akielaries/signalmesh/modules/apm/bsp/bsp.c

#include <stddef.h>

#include "hal.h"
#include "ch.h"

#include "bsp/bsp.h"

#include "bsp/utils/bsp_gpt.h"
#include "bsp/utils/bsp_io.h"

#include "bsp/configs/bsp_uart_config.h"
#include "bsp/configs/bsp_i2c_config.h"
#include "bsp/configs/bsp_spi_config.h"

#include "drivers/driver_registry.h"
#include "drivers/driver_api.h"

#include "drivers/ina219.h"
#include "drivers/ina3221.h"
#include "drivers/bme280.h"
#include "drivers/bh1750.h"
#include "drivers/aht2x.h"
#include "drivers/24lc256.h"
#include "drivers/w25qxx.h"
#include "drivers/servo.h"
#include "drivers/gm009605.h"
#include "drivers/lcd2004.h"

#include "version_gen.h" // generated: FW_VERSION_STRING etc.



// private data for ina219
static ina219_t ina219_dev_data[2];
// private data for ina3221
static ina3221_t ina3221_dev_data;
// private data for bme280
// static bme280_t bme280_dev_data; // BME280 driver doesn't have a private data struct
// private data for bh1750
static bh1750_t bh1750_dev_data;
static aht2x_t aht2x_dev_data;
static eeprom_24lc256_t eeprom_24lc256_dev_data;
// private data for w25qxx
static w25qxx_t w25qxx_dev_data_1;
static w25qxx_t w25qxx_dev_data_2;
// private data for servo
// static servo_t servo_dev_data; // servo driver doesn't have a private data struct
// private data for gm009605
static gm009605_t gm009605_dev_data;
static lcd2004_t lcd2004_dev_data;


// array of devices present on APM
device_t board_devices[] = {
    {
        .name = "ina219_main",
        .driver = &ina219_driver,
        .bus = &I2CD1,
        .addr = 0x40,
        .priv = &ina219_dev_data[0],
        .is_active = true
    },
    {
        .name = "ina219_aux",
        .driver = &ina219_driver,
        .bus = &I2CD1,
        .addr = 0x45, // A0 and A1 pins grounded
        .priv = &ina219_dev_data[1],
        .is_active = true
    },
    {
        .name = "ina3221",
        .driver = &ina3221_driver,
        .bus = &I2CD1,
        .addr = 0x40, // Note: This may conflict with ina219_main
        .priv = &ina3221_dev_data,
        .is_active = false
    },
    {
        .name = "aht2x",
        .driver = &aht2x_driver,
        .bus = &I2CD1,
        .addr = 0x38,
        .priv = &aht2x_dev_data,
        .is_active = false
    },
    {
        .name = "bme280",
        .driver = &bme280_driver,
        .bus = &I2CD1,
        .addr = 0x76,
        .priv = NULL,
        .is_active = false
    },
    {
        .name = "bh1750",
        .driver = &bh1750_driver,
        .bus = &I2CD1,
        .addr = 0x23,
        .priv = &bh1750_dev_data,
        .is_active = false
    },
    {
        .name = "24lc256",
        .driver = &eeprom_24lc256_driver,
        .bus = &I2CD1,
        .addr = 0x50,
        .priv = &eeprom_24lc256_dev_data,
        .is_active = false
    },
    {
        .name = "w25qxx_1",
        .driver = &w25qxx_driver,
        .bus = &spi_bus_w25qxx_1,
        .addr = 0, // SPI uses CS pin, not address
        .priv = &w25qxx_dev_data_1,
        .is_active = false
    },
    {
        .name = "w25qxx_2",
        .driver = &w25qxx_driver,
        .bus = &spi_bus_w25qxx_2,
        .addr = 0, // SPI uses CS pin, not address
        .priv = &w25qxx_dev_data_2,
        .is_active = false
    },
    {
        .name = "gm009605",
        .driver = &gm009605_driver,
        .bus = &I2CD1,
        .addr = 0x3C,
        .priv = &gm009605_dev_data,
        .is_active = true
    },
    {
        .name = "lcd2004",
        .driver = &lcd2004_driver,
        .bus = &I2CD1,
        .addr = 0x26,          // PCF8574 backpack on this module lands at 0x26 (not the 0x27 default)
        .priv = &lcd2004_dev_data,
        .is_active = true
    },
    /*
    {
        .name = "servo",
        .driver = &servo_driver,
        .bus = NULL,
        .priv = NULL,
        .is_active = false
    },
    */
};


// number of devices on APM
const size_t num_board_devices = sizeof(board_devices) / sizeof(board_devices[0]);


// onboard-LED heartbeat: a low-priority "is it alive" sweep over the three
// nucleo user LEDs. started by bsp_init, not from app main
static const ioline_t heartbeat_leds[] = {
  LINE_LED_GREEN,
  LINE_LED_YELLOW,
  LINE_LED_RED,
};

static THD_WORKING_AREA(wa_heartbeat, 256);
static THD_FUNCTION(heartbeat_thread, arg) {
  (void)arg;
  chRegSetThreadName("heartbeat");

  const size_t n = sizeof(heartbeat_leds) / sizeof(heartbeat_leds[0]);
  for (size_t i = 0; i < n; i++) {
    palSetLineMode(heartbeat_leds[i], PAL_MODE_OUTPUT_PUSHPULL);
    palClearLine(heartbeat_leds[i]);
  }

  // sweep one LED at a time so the cycle shows the scheduler is alive
  size_t cur = 0;
  while (true) {
    palSetLine(heartbeat_leds[cur]);
    chThdSleepMilliseconds(500);
    palClearLine(heartbeat_leds[cur]);
    cur = (cur + 1U) % n;
  }
}

static void heartbeat_start(void) {
  chThdCreateStatic(wa_heartbeat, sizeof(wa_heartbeat),
                    LOWPRIO, heartbeat_thread, NULL);
}


void bsp_init(void) {
  halInit();
  chSysInit();

  // initialize debug UART
  bsp_io_init();

  bsp_printf("\n...Starting...\n\n");
  bsp_printf("%s\n", FW_VERSION_STRING); // e.g. APM v1.0.0-7e98556-dirty

  bsp_printf("booting...");
  for (uint8_t i = 0; i < 3; i++) {
    bsp_printf(".");
    chThdSleepMilliseconds(250);
  }
  bsp_printf("\n");

  // chip info
  bsp_printf("System tick freq: %u Hz\n", CH_CFG_ST_FREQUENCY);
  bsp_printf("DBGMCU->IDCODE: 0x%08lX\r\n", DBGMCU->IDCODE);
  bsp_printf("REV_ID: 0x%X\r\nDEV_ID: 0x%X\n", DBGMCU->IDCODE >> 16,
                                            DBGMCU->IDCODE & 0xFFF);

  // initialize drivers this board supports
  bsp_i2c_init();
  bsp_printf("I2C initialized\n");

  bsp_spi_init();
  bsp_printf("SPI initialized\n");

  init_devices();
  bsp_printf("initialized devices\n");

/*
  // these should be configured more elegantly like how the i2c stuff is configured
  // ADC inputs
  palSetPadMode(GPIOB, 1, PAL_MODE_INPUT_ANALOG); // PB1, ADC channel 5
  palSetPadMode(GPIOA, 3, PAL_MODE_INPUT_ANALOG); // PA3, ADC channel 15
  palSetPadMode(GPIOC, 0, PAL_MODE_INPUT_ANALOG); // PC0, ADC channel 10
  palSetPadMode(GPIOC, 3, PAL_MODE_INPUT_ANALOG); // PC3, ADC channel 13

  // PWM on PE11, timer 1 channel 2?
  palSetPadMode(GPIOE, 11, PAL_MODE_ALTERNATE(1));
*/

  heartbeat_start();
  bsp_printf("heartbeat thread started\n");

  bsp_printf("End of BSP init\n\r\n");
}
