akielaries/signalmesh/modules/afm/mcu/bsp/drivers/inc/GOWIN_M1_spi.h

/*
 ******************************************************************************************
 * @file      GOWIN_M1_spi.h
 * @author    GowinSemicoductor
 * @device    Gowin_EMPU_M1
 * @brief     This file contains all the functions prototypes for the SPI firmware library.
 ******************************************************************************************
 */

/* Define to prevent recursive inclusion -------------------------------------*/
#ifndef GOWIN_M1_SPI_H
#define GOWIN_M1_SPI_H

#ifdef __cplusplus
 extern "C" {
#endif

/* Includes ------------------------------------------------------------------*/
#include "GOWIN_M1.h"

/** @addtogroup GOWIN_M1_StdPeriph_Driver
  * @{
  */
/** @addtogroup SPI
  * @{
  */

/******************************************************************************/
/*                  Serial Peripheral Interface (SPI)                         */
/******************************************************************************/
/* bit definitions for CTRL register */
#define SPI_CR_DIRECTION           ((uint32_t) 0x00000001)    /* DIRECTION              */
#define SPI_CR_PHASE               ((uint32_t) 0x00000002)    /* PHASE                  */
#define SPI_CR_POLARITY            ((uint32_t) 0x00000004)    /* POLARITY               */
#define SPI_CR_CLKSEL              ((uint32_t) 0x00000018)    /* CLKSEL                 */

/* bit definitions for STATUS register */
#define SPI_STATUS_ROE             ((uint32_t) 0x00000004)    /* Receive Overrun Error  */
#define SPI_STATUS_TOE             ((uint32_t) 0x00000008)    /* Transmit Overrun Error */
#define SPI_STATUS_TMT             ((uint32_t) 0x00000010)    /* Transmitting           */
#define SPI_STATUS_TRDY            ((uint32_t) 0x00000020)    /* Transmit Ready         */
#define SPI_STATUS_RRDY            ((uint32_t) 0x00000040)    /* Receive Ready          */
#define SPI_STATUS_ERR             ((uint32_t) 0x00000080)    /* Error                  */

/**
  * @}
  */

/** @defgroup SPI_Exported_Types
  * @{
  */

/* SPI InitTypeDef */
typedef struct
{
  uint8_t  DIRECTION;  // 0: msb first; 1: lsb first
  uint8_t  PHASE;      // 0: sample at posedge edge; 1: sample at negedge.
  uint8_t  POLARITY;   // 0: idle sclk low; 1: idle sclk high
  uint8_t  CLKSEL;     // clk div = (clksel + 1) * 2
}SPI_InitTypeDef;

/**
  * @}
  */

/** @defgroup SPI_Exported_Macros
  * @{
  */

/* Clock Selection */
#define CLKSEL_CLK_DIV_2   ((uint32_t) 0x00000000)  //CLK/2
#define CLKSEL_CLK_DIV_4   ((uint32_t) 0x00000001)  //CLK/4
#define CLKSEL_CLK_DIV_6   ((uint32_t) 0x00000002)  //CLK/6
#define CLKSEL_CLK_DIV_8   ((uint32_t) 0x00000003)  //CLK/8

#define SHIFT_DIR_MSB_FIRST      (0)
#define SHIFT_DIR_LSB_FIRST      (1)

#define SPI_CPOL_LO              (0) 
#define SPI_CPOL_HI              (1)

#define SPI_CPHA_POSEDGE         (0)
#define SPI_CPHA_NEGEDGE         (1)

/* Register Bit Position */
#define SPI_CR_DIRECTION_Pos   0   /* CTRL register DIRECTION bit position */
#define SPI_CR_PHASE_Pos       1   /* CTRL register PHASE bit position     */
#define SPI_CR_POLARITY_Pos    2   /* CTRL register POLARITY bit position  */
#define SPI_STATUS_ROE_Pos     2   /* STATUS register ROE bit position     */
#define SPI_STATUS_TOE_Pos     3   /* STATUS register TOE bit position     */
#define SPI_STATUS_TMT_Pos     4   /* STATUS register TMT bit position     */
#define SPI_STATUS_TRDY_Pos    5   /* STATUS register TRDY bit position    */
#define SPI_STATUS_RRDY_Pos    6   /* STATUS register RRDY bit position    */
#define SPI_STATUS_ERR_Pos     7   /* STATUS register ERR bit position     */

#define SPI_CR_CLKSEL_Pos     ((uint32_t) 0x00000003)    /* CTRL register CLKSEL Position */
#define SPI_CR_CLKSEL_Mask    ((uint32_t) 0x00000003)    /* CTRL register CLKSEL mask     */

#define SELECT_SPI            {SPI->SSMASK = 1;}
#define DESELECT_SPI          {SPI->SSMASK = 0;}


/**
  * @}
  */

/** @defgroup SPI_Exported_Functions
  * @{
  */

/**
  * @brief Initializes SPI
  */
extern void SPI_Init(SPI_InitTypeDef* SPI_InitStruct);

/**
  * @brief Sets Direction
  */
extern void SPI_SetDirection(void);

/**
  * @brief Clears Direction
  */
extern void SPI_ClrDirection(void);

/**
  * @brief Returns Direction
  */
extern uint32_t SPI_GetDirection(void);

/**
  * @brief Sets Phase
  */
extern void SPI_SetPhase(void);

/**
  * @brief Clears Phase
  */
extern void SPI_ClrPhase(void);

/**
  * @brief Returns Phase
  */
extern uint32_t SPI_GetPhase(void);

/**
  * @brief Returns Polarity
  */
extern uint32_t SPI_GetPolarity(void);

/**
  * @brief Clears Polarity
  */
extern void SPI_ClrPolarity(void);

/**
  * @brief Sets Polarity
  */
extern void SPI_SetPolarity(void);

/**
  * @brief Sets ClkSel
  */
extern void SPI_SetClkSel(uint32_t clksel);

/**
  * @brief Returns ClkSel
  */
extern uint32_t SPI_GetClkSel(void);

/**
  * @brief Reads transmit overrun error status
  */
extern FlagStatus SPI_GetToeStatus(void);

/**
  * @brief Reads receive overrun error status
  */
extern FlagStatus SPI_GetRoeStatus(void);

/**
  * @brief Reads transmitting status
  */
extern FlagStatus SPI_GetTmtStatus(void);

/**
  * @brief Reads transmit ready status
  */
extern FlagStatus SPI_GetTrdyStatus(void);

/**
  * @brief Reads receive ready status
  */
extern FlagStatus SPI_GetRrdyStatus(void);

/**
  * @brief Reads error status
  */
extern FlagStatus SPI_GetErrStatus(void);

/**
  * @brief Clears transmit overrun error status
  */
extern void SPI_ClrToeStatus(void);

/**
  * @brief Clear receive overrun error status
  */
extern void SPI_ClrRoeStatus(void);

/**
  * @brief Clears error status
  */
extern void SPI_ClrErrStatus(void);

/**
  * @brief Reads and Writes Byte Data
  */
extern uint8_t SPI_ReadWriteByte(uint8_t cmd);

/**
  * @brief Writes Data
  */
extern void SPI_WriteData(uint8_t data);

/**
  * @brief Reads Data
  */
extern uint8_t SPI_ReadData(void);

/**
  * @brief SPI_Slave Select
  */
extern  void SPI_Select_Slave(uint32_t Slave_address);

#ifdef __cplusplus
}
#endif

#endif /* GOWIN_M1_SPI_H */

/**
  * @}
  */

/**
  * @}
  */
