akielaries/signalmesh/modules/afm/rtl/sine_wave_gen.v

/*
 * Sine Wave Generator Example for Gowin FPGAs
 *
 * This module demonstrates how to generate a sine wave using Pulse Width
 * Modulation (PWM). It produces a 30 kHz sine wave from a 27 MHz master clock.
 *
 * IMPORTANT: The output of this module is a PWM signal. To see an analog
 * sine wave, you MUST connect an external low-pass RC filter to the
 * output pin (bank2_3v3_waveform). A 1k Ohm resistor followed by a
 * 3.3nF capacitor to ground is a good starting point.
 */

module sine_wave_gen (
  // --- Inputs ---
  input bank1_3v3_xtal_in, // Input clock from the crystal oscillator (27 MHz)
  input bank3_1v8_sys_rst, // Active-low reset

  // --- Outputs ---
  output bank1_3v3_xtal_route,
  output bank2_3v3_waveform // The PWM signal output
);

  // --- Port Aliases (standard Verilog via wire/assign) ---
  wire clk;
  wire rst_n;

  assign clk = bank1_3v3_xtal_in;
  assign bank1_3v3_xtal_route = bank1_3v3_xtal_in;
  assign rst_n = bank3_1v8_sys_rst;
  // --------------------------------------------------------

  // --- Phase Accumulator for LUT Index ---
  // This steps through the sine lookup table at a rate that produces
  // the desired output frequency.
  // F_out = (F_clk * Step_inc) / (2^32)
  // Step_inc = (F_out * 2^32) / F_clk
  //          = (30,000 * 2^32) / 27,000,000 = 4772186
  localparam PHASE_INCREMENT = 32'd4772186;
  
  reg [31:0] phase_accumulator;
  always @(posedge clk or negedge rst_n) begin
    if (!rst_n) begin
      phase_accumulator <= 32'd0;
    end else begin
      phase_accumulator <= phase_accumulator + PHASE_INCREMENT;
    end
  end

  // Use the top 8 bits of the accumulator as the address for our 256-entry table.
  wire [7:0] lut_address = phase_accumulator[31:24];


  // --- Sine Wave Lookup Table (LUT) ---
  // This is a 256-entry, 8-bit Read-Only Memory (ROM) that stores one
  // cycle of a sine wave. The values range from 0 to 255.
  reg [7:0] lut_value;
  always @(*) begin
    case (lut_address)
      8'd0:   lut_value = 8'd128;
      8'd1:   lut_value = 8'd131;
      8'd2:   lut_value = 8'd134;
      8'd3:   lut_value = 8'd137;
      8'd4:   lut_value = 8'd140;
      8'd5:   lut_value = 8'd143;
      8'd6:   lut_value = 8'd146;
      8'd7:   lut_value = 8'd149;
      8'd8:   lut_value = 8'd152;
      8'd9:   lut_value = 8'd155;
      8'd10:  lut_value = 8'd158;
      8'd11:  lut_value = 8'd161;
      8'd12:  lut_value = 8'd164;
      8'd13:  lut_value = 8'd167;
      8'd14:  lut_value = 8'd170;
      8'd15:  lut_value = 8'd173;
      8'd16:  lut_value = 8'd176;
      8'd17:  lut_value = 8'd179;
      8'd18:  lut_value = 8'd182;
      8'd19:  lut_value = 8'd185;
      8'd20:  lut_value = 8'd188;
      8'd21:  lut_value = 8'd190;
      8'd22:  lut_value = 8'd193;
      8'd23:  lut_value = 8'd196;
      8'd24:  lut_value = 8'd198;
      8'd25:  lut_value = 8'd201;
      8'd26:  lut_value = 8'd203;
      8'd27:  lut_value = 8'd206;
      8'd28:  lut_value = 8'd208;
      8'd29:  lut_value = 8'd211;
      8'd30:  lut_value = 8'd213;
      8'd31:  lut_value = 8'd215;
      8'd32:  lut_value = 8'd217;
      8'd33:  lut_value = 8'd219;
      8'd34:  lut_value = 8'd221;
      8'd35:  lut_value = 8'd223;
      8'd36:  lut_value = 8'd225;
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
      8'd249: lut_value = 8'd107;
      8'd250: lut_value = 8'd110;
      8'd251: lut_value = 8'd113;
      8'd252: lut_value = 8'd116;
      8'd253: lut_value = 8'd119;
      8'd254: lut_value = 8'd122;
      8'd255: lut_value = 8'd125;
      default: lut_value = 8'd128;
    endcase
  end

  // --- PWM Generator ---
  // This creates a high-frequency square wave whose duty cycle is
  // controlled by the value from the sine LUT.
  reg [7:0] pwm_counter;
  always @(posedge clk or negedge rst_n) begin
    if (!rst_n) begin
      pwm_counter <= 8'd0;
    end else begin
      // The counter continuously cycles from 0-255
      pwm_counter <= pwm_counter + 1'b1;
    end
  end

  // The output is high when the counter is less than the sine value.
  // This creates the variable duty cycle.
  assign bank2_3v3_waveform = (pwm_counter < lut_value);

endmodule
