akielaries/signalmesh/modules/acm/acm_fpga/rtl/sine_lut.v

// generated: 256-entry, one-period, 12-bit unsigned sine ROM (centered 2048)
module sine_lut (input wire [7:0] addr, output reg [11:0] data);
  always @(*) begin
    case (addr)
      8'd0  : data = 12'd2048;
      8'd1  : data = 12'd2098;
      8'd2  : data = 12'd2148;
      8'd3  : data = 12'd2199;
      8'd4  : data = 12'd2249;
      8'd5  : data = 12'd2299;
      8'd6  : data = 12'd2348;
      8'd7  : data = 12'd2398;
      8'd8  : data = 12'd2447;
      8'd9  : data = 12'd2497;
      8'd10 : data = 12'd2545;
      8'd11 : data = 12'd2594;
      8'd12 : data = 12'd2642;
      8'd13 : data = 12'd2690;
      8'd14 : data = 12'd2738;
      8'd15 : data = 12'd2785;
      8'd16 : data = 12'd2831;
      8'd17 : data = 12'd2878;
      8'd18 : data = 12'd2923;
      8'd19 : data = 12'd2968;
      8'd20 : data = 12'd3013;
      8'd21 : data = 12'd3057;
      8'd22 : data = 12'd3100;
      8'd23 : data = 12'd3143;
      8'd24 : data = 12'd3185;
      8'd25 : data = 12'd3227;
      8'd26 : data = 12'd3267;
      8'd27 : data = 12'd3307;
      8'd28 : data = 12'd3347;
      8'd29 : data = 12'd3385;
      8'd30 : data = 12'd3423;
      8'd31 : data = 12'd3459;
      8'd32 : data = 12'd3495;
      8'd33 : data = 12'd3531;
      8'd34 : data = 12'd3565;
      8'd35 : data = 12'd3598;
      8'd36 : data = 12'd3630;
      8'd37 : data = 12'd3662;
      8'd38 : data = 12'd3692;
      8'd39 : data = 12'd3722;
      8'd40 : data = 12'd3750;
      8'd41 : data = 12'd3777;
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
      8'd249: data = 12'd1698;
      8'd250: data = 12'd1748;
      8'd251: data = 12'd1797;
      8'd252: data = 12'd1847;
      8'd253: data = 12'd1897;
      8'd254: data = 12'd1948;
      8'd255: data = 12'd1998;
      default: data = 12'd2048;
    endcase
  end
endmodule
