akielaries/signalmesh/modules/afm/fpga/src/gowin_empu_m1/temp/gw_empu_m1/cm1_option_defs.v

`define CM1_NUM_IRQ 32
`define CM1_OS 1
`define CM1_SMALL_MUL 0
`define CM1_BE8 0
`define CM1_JTAG 0
`define CM1_SW 1
`define CM1_SMALL_DEBUG 0
`define CM1_ITCM_LA_EN 1
`define CM1_ITCM_UA_EN 0
`define CM1_ITCMSIZE 4'b0101
`define CM1_DTCMSIZE 4'b0101
