akielaries/signalmesh/modules/afm/mcu/bsp/drivers/inc/GOWIN_M1_rtc.h

/*
 ******************************************************************************************
 * @file      GOWIN_M1_rtc.h
 * @author    GowinSemicoductor
 * @device    Gowin_EMPU_M1
 * @brief     This file contains all the functions prototypes for the RTC firmware library.
 ******************************************************************************************
 */

/* Define to prevent recursive inclusion -------------------------------------*/
#ifndef GOWIN_M1_RTC_H
#define GOWIN_M1_RTC_H

#ifdef __cplusplus
 extern "C" {
#endif

/* Includes ------------------------------------------------------------------*/
#include <stdint.h>
#include "GOWIN_M1.h"

/* Functions ------------------------------------------------------------------*/
extern uint32_t Get_Current_Value(void);
extern void Set_Match_Value(uint32_t match_value);
extern uint32_t Get_Match_Value(void);
extern void Set_Load_Value(uint32_t load_value);
extern uint32_t Get_Load_Value(void);
extern void Start_RTC(void);
extern void Close_RTC(void);
extern void RTC_Inter_Mask_Set(void);
extern uint8_t Get_RTC_Control_value(void);
extern void RTC_Inter_Mask_Clr(void);
extern uint8_t Get_RTC_Inter_Mask_value(void);
extern void Clear_RTC_interrupt(void);
extern void RTC_init(void);

#ifdef __cplusplus
}
#endif

#endif /* GOWIN_M1_RTC_H */
