akielaries/signalmesh/modules/afm/mcu/bsp/system/system_GOWIN_M1.c

/*
 *******************************************************************************************
 * @file      system_GOWIN_M1.c
 * @author    GowinSemicoductor
 * @device    Gowin_EMPU_M1
 * @brief     CMSIS Cortex-M1 Device Peripheral Access Layer System Source File.
 *            This file contains the system clock configuration for Cortex-M1 device.
 *
 *            This file provides two functions and one global variable to be called from
 *            user application:
 *              - SystemInit(): Setups the system clock.
 *                              This function is called at startup just after reset and
 *                              before branch to main program. This call is mad inside
 *                              the "startup_GOWIN_M1.s" file.
 *              - SystemCoreClock variable: Contains the core clock, it can be used
 *                              by the user application to setup the SysTick 
 *                              timer or configure other parameters.
 *              - SystemCoreClockUpdate(): Updates the variable SystemCoreClock and must
 *                              be called whenever the core clock is changed
 *                              during program execution.
 *******************************************************************************************
 */

/* Includes ------------------------------------------------------------------*/
#include "GOWIN_M1.h"

/*----------------------------------------------------------------------------
  Define clocks
 *----------------------------------------------------------------------------*/
#define  XTAL            (100000000UL)     /* Oscillator frequency */

#define  SYSTEM_CLOCK    (XTAL / 2U)       /* 50MHz                */


/*----------------------------------------------------------------------------
  System Core Clock Variable
 *----------------------------------------------------------------------------*/
unsigned int SystemCoreClock = SYSTEM_CLOCK;  /* System Core Clock Frequency */


/*----------------------------------------------------------------------------
  System Core Clock update function
 *----------------------------------------------------------------------------*/
/**
 * Update SystemCoreClock variable
 *
 * @param  none
 * @return none
 * @brief  Updates the SystemCoreClock with current core Clock retrieved from cpu registers.
 */
void SystemCoreClockUpdate (void)
{
  SystemCoreClock = SYSTEM_CLOCK;
}

/*----------------------------------------------------------------------------
  System initialization function
 *----------------------------------------------------------------------------*/
/**
 * @param  none
 * @return none
 * @brief  Setup the Cortex-M1 system.
 *         Initialize the System.
 */
void SystemInit (void)
{
  SystemCoreClock = SYSTEM_CLOCK;
}
