akielaries/signalmesh/modules/afm/mcu/src/delay.h

#ifndef __DELAY_H_
#define __DELAY_H_


#include <stdint.h>


void delay_init(void);					//Initializes
void delay_us(uint32_t nus);		//Delay microsecond
void delay_ms(uint16_t nms);		//Delay milliseconds
void delay_sec(uint16_t sec);		//Delay seconds


#endif	/* __DELAY_H_ */
