akielaries/signalmesh/modules/apm/bsp/include/bsp_defs.h

/**
 * @brief generic definitions for buttons, leds, etc
 */


#define APM_BSP_WARN  LINE_LED_YELLOW
#define APM_BSP_ERR   LINE_LED_RED
#define APM_BSP_OK    LINE_LED_GREEN

#define APM_BSP_BUTTON LINE_BUTTON
